keyquesttech/Enclave/imgs/36.PNG

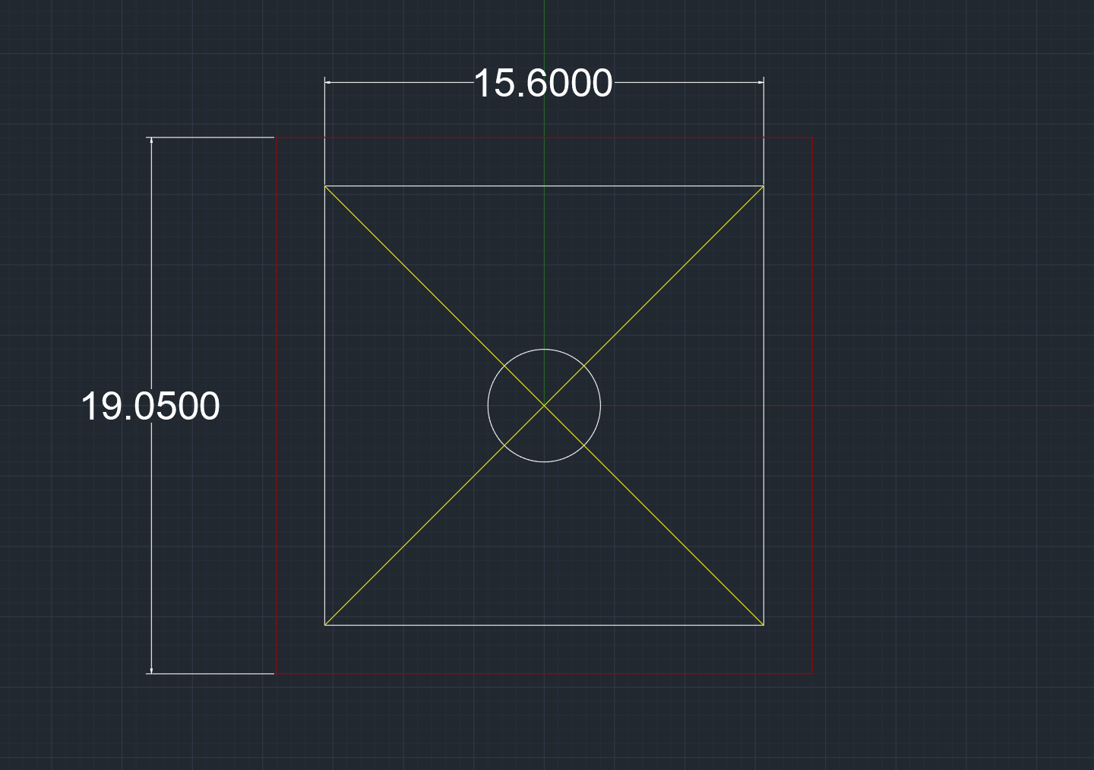
imgs/36.PNG
