keyquesttech/Enclave/imgs/37.PNG

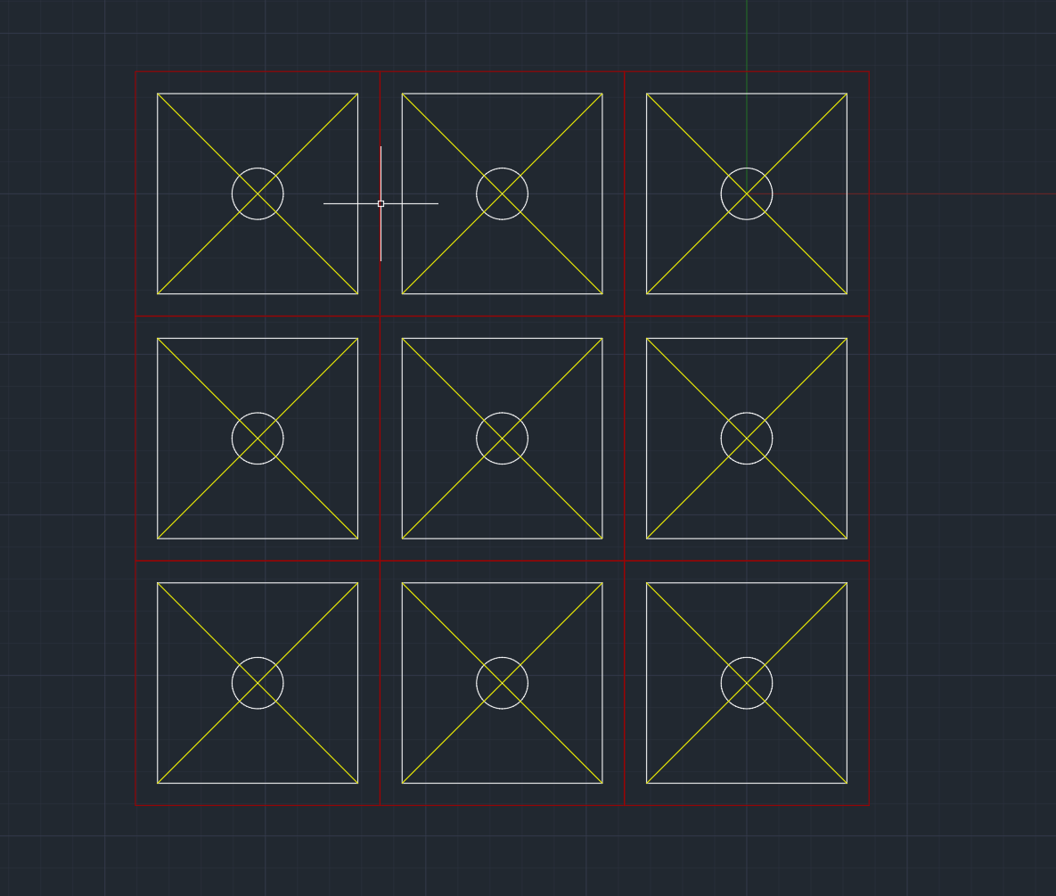
imgs/37.PNG
