keyquesttech/Enclave/imgs/38.PNG

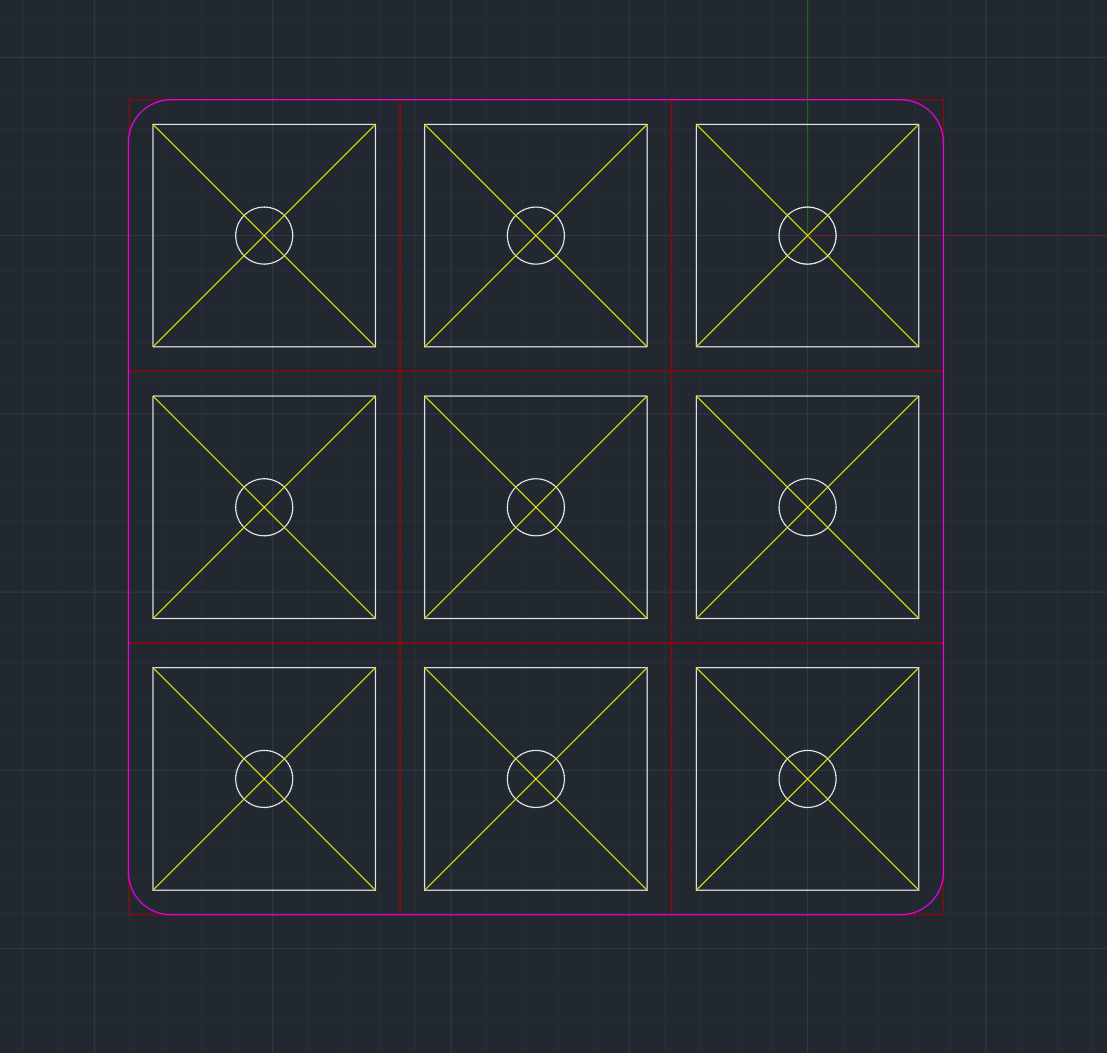
imgs/38.PNG
