keyquesttech/Enclave/imgs/39.PNG

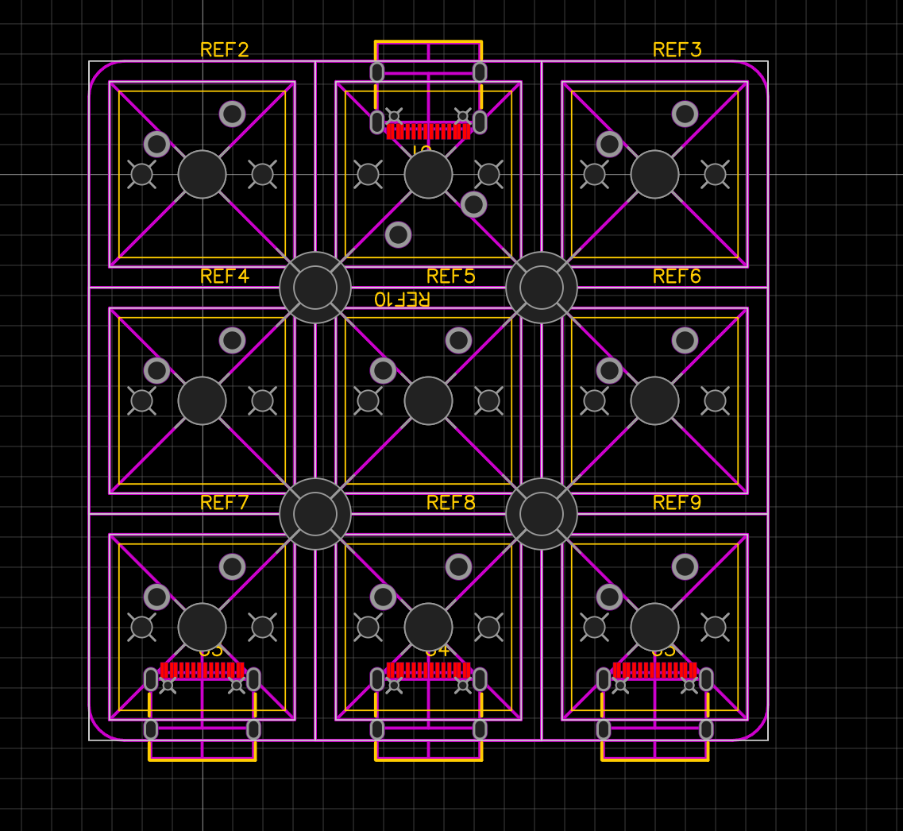
imgs/39.PNG
