keyquesttech/Enclave/imgs/40.PNG

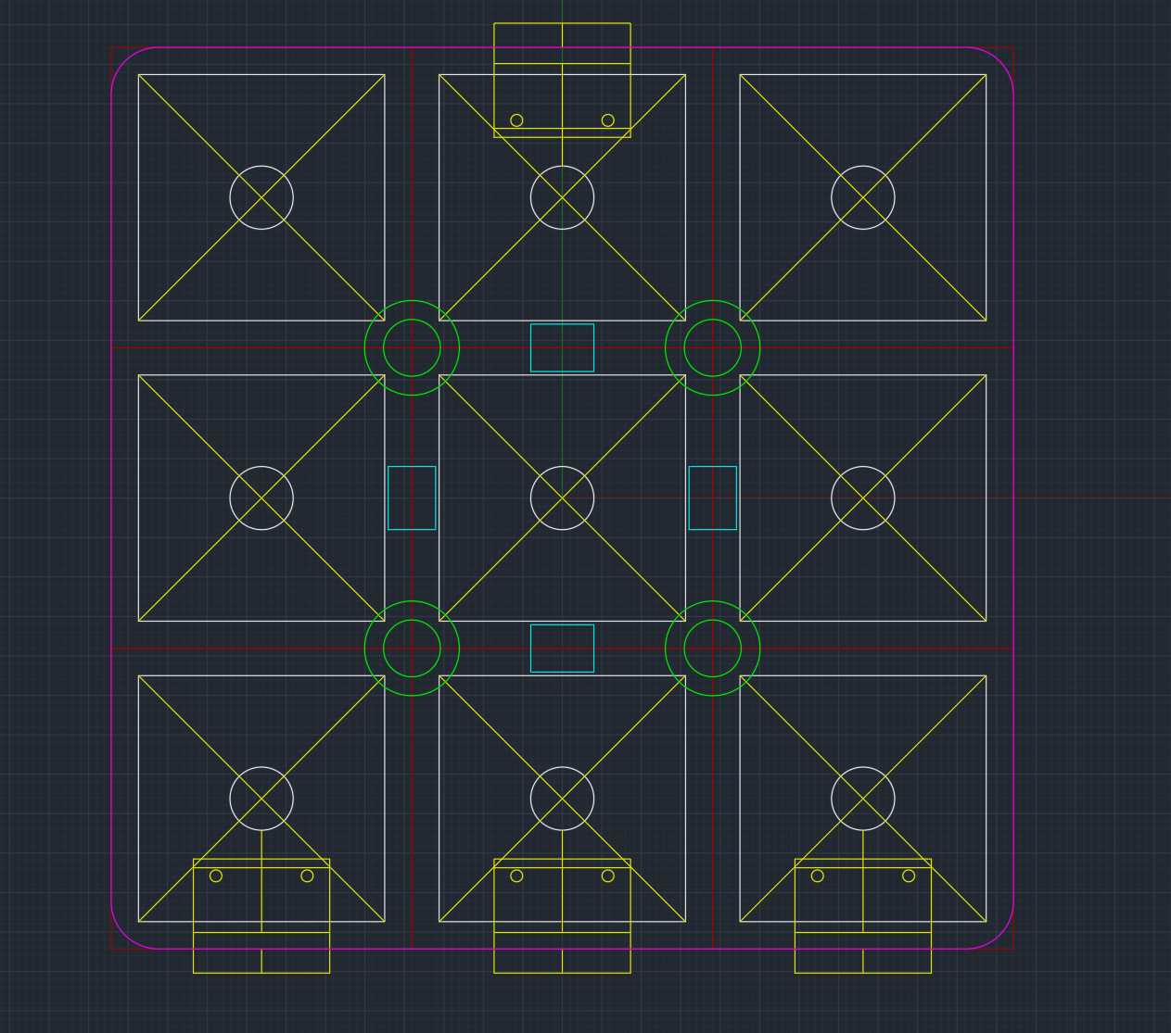
imgs/40.PNG
