keyquesttech/Enclave/imgs/41.jpg

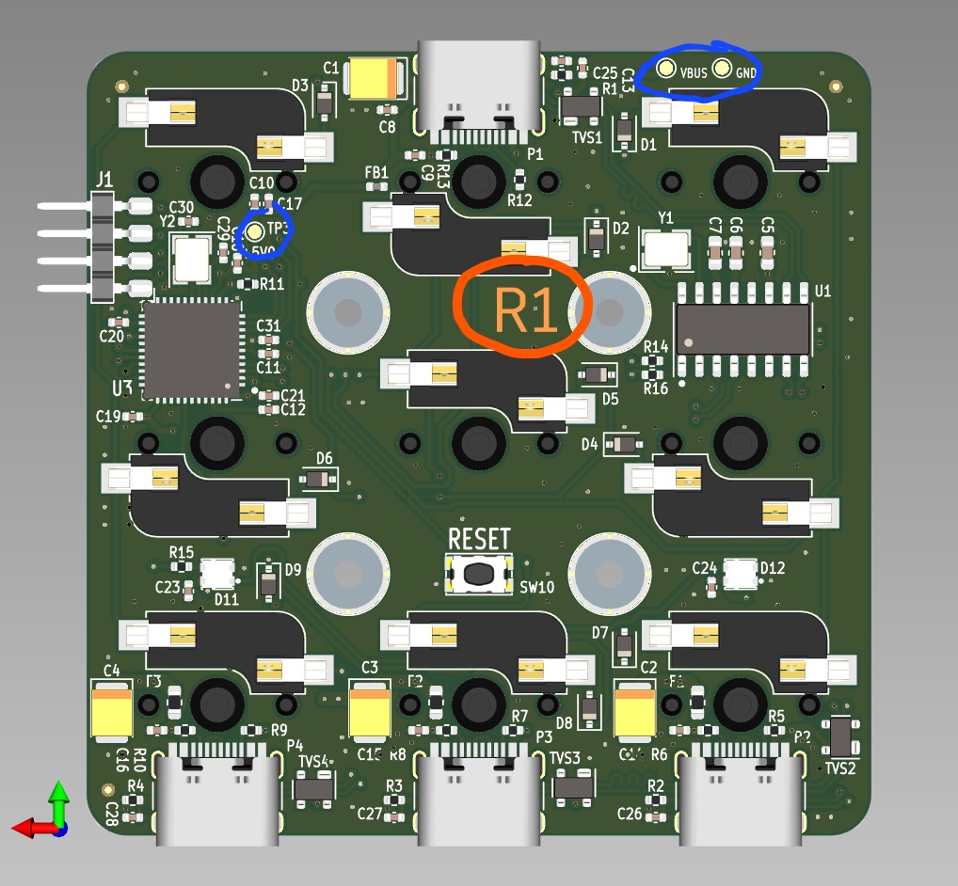
imgs/41.jpg
