keyquesttech/Enclave/imgs/75.jpg

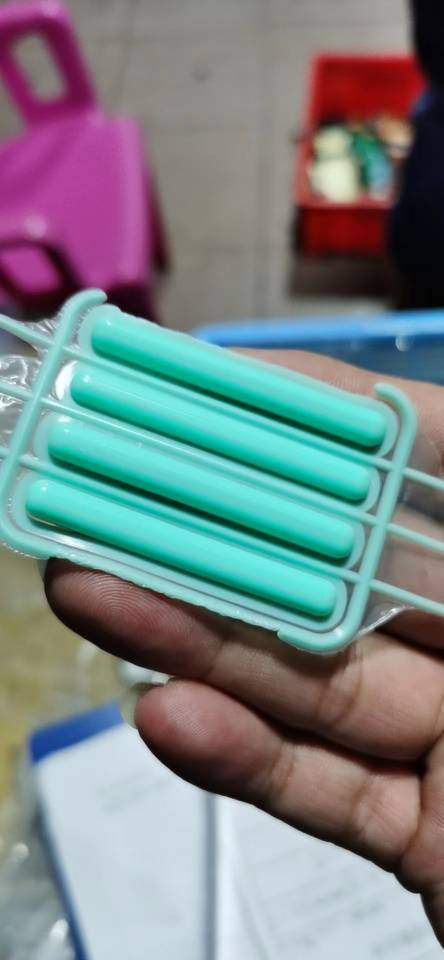
imgs/75.jpg
