keyquesttech/Enclave/imgs/77.png

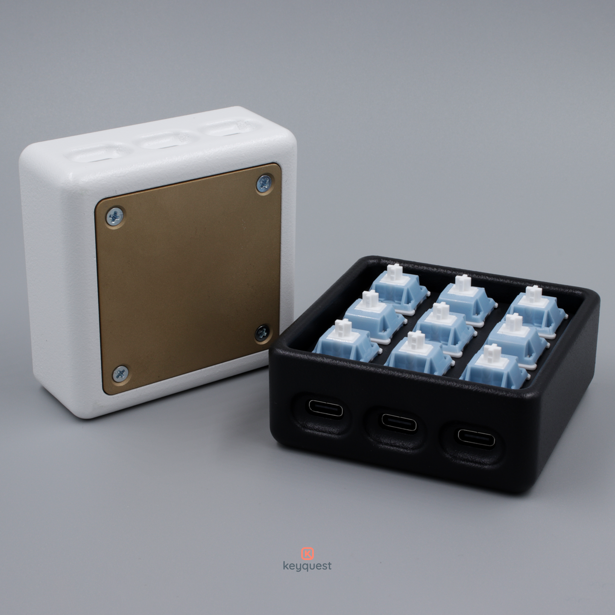
imgs/77.png
