keyquesttech/Enclave/imgs/78.png

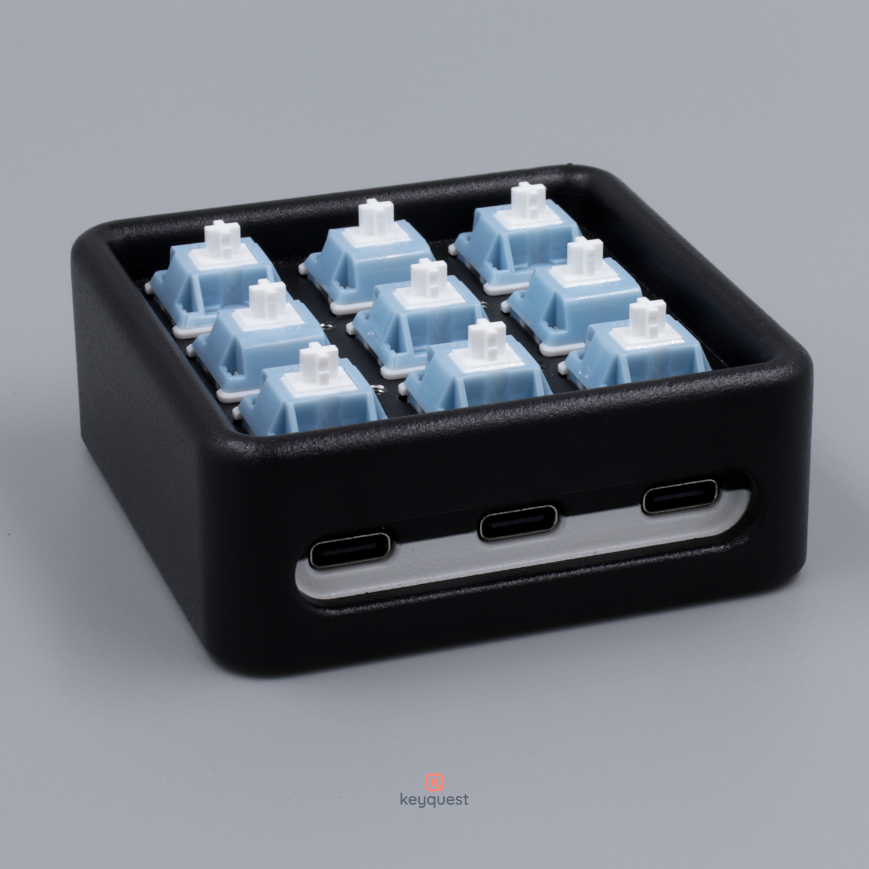
imgs/78.png
