keyquesttech/Enclave/imgs/79.png

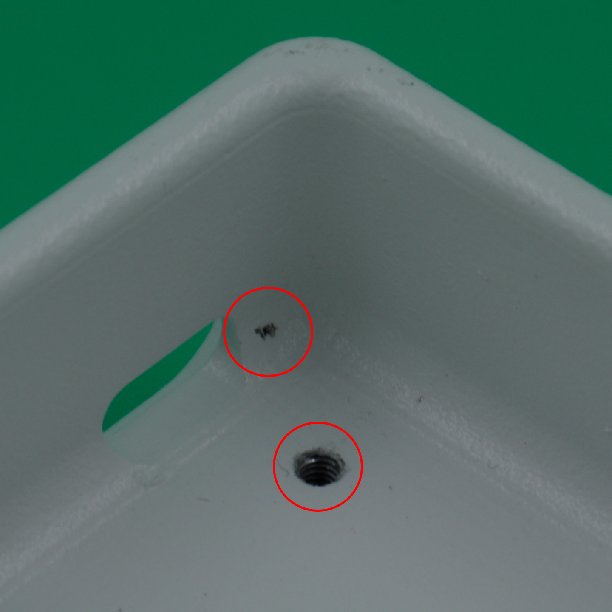
imgs/79.png
