keyquesttech/Enclave/imgs/83.jpg

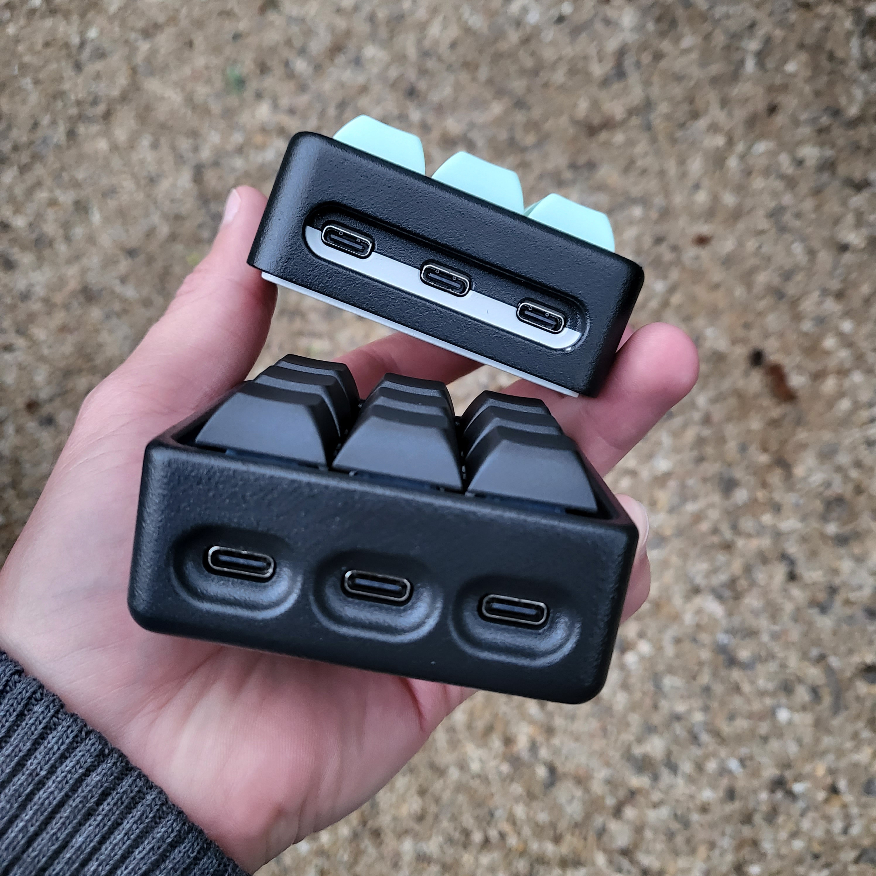
imgs/83.jpg
