keyquesttech/Enclave/imgs/84.PNG

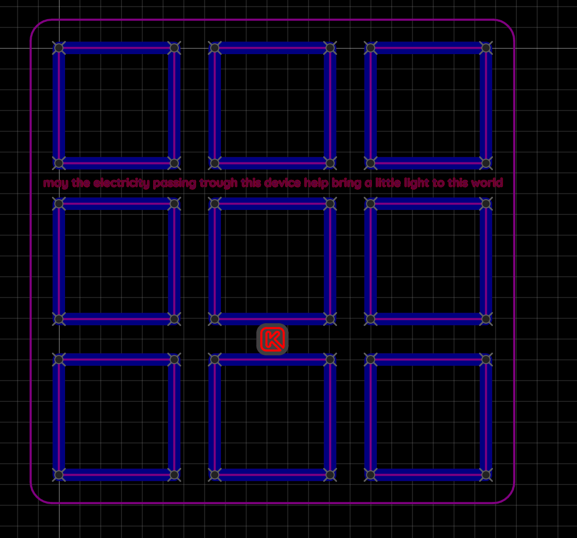
imgs/84.PNG
