keyquesttech/Enclave/imgs/Outline_preview.png

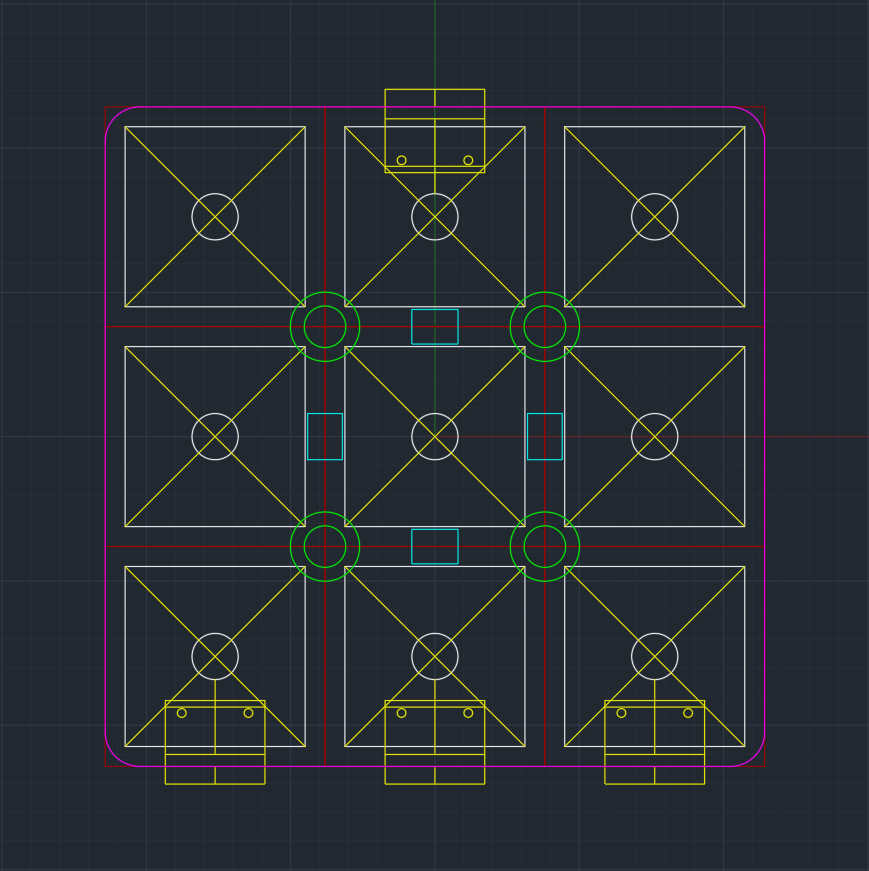
imgs/Outline_preview.png
