keyquesttech/Enclave/imgs/PCB_Mockup.PNG

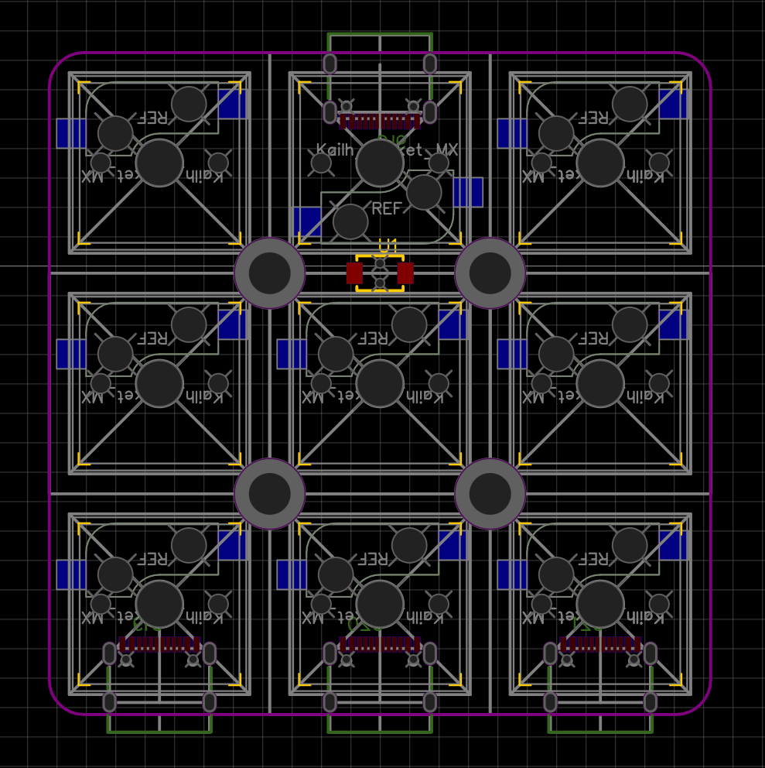
imgs/PCB_Mockup.PNG
