keyquesttech/Enclave/Topo/KiCad_SRC/Topo_v0.kicad_sch

## KiCad design Topo/KiCad_SRC/Topo_v0.kicad_sch (2023-02-13)

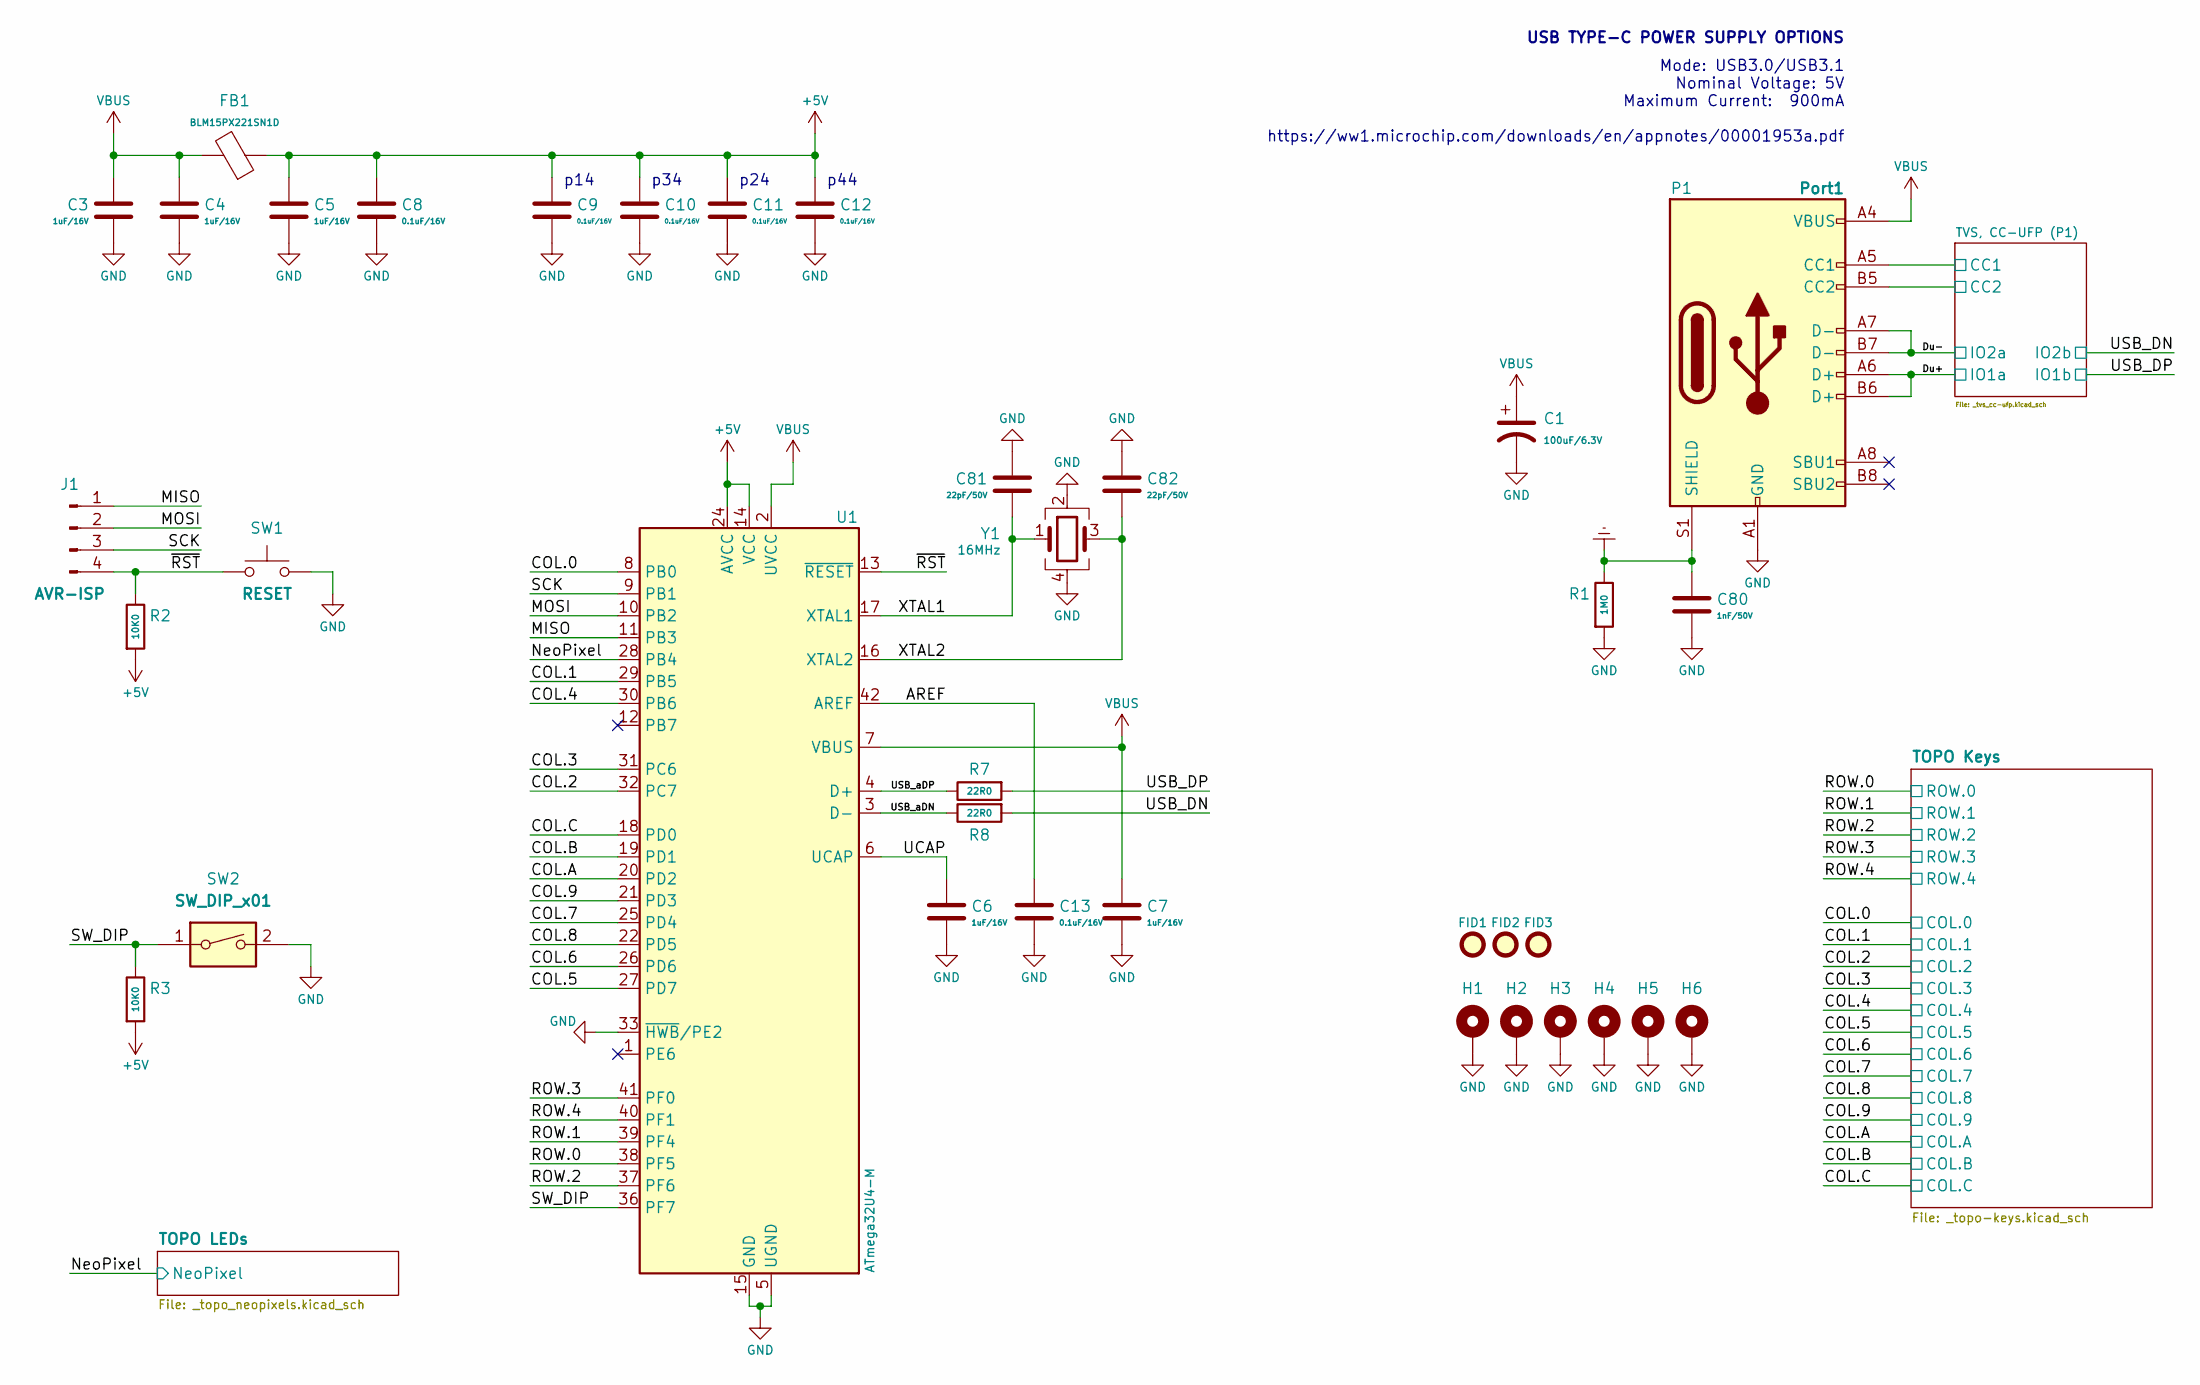
[picture p47: schematic Topo_v0.kicad_sch]

Parts:
C1: 100uF/6.3V; CP_EIA-3528-12_Kemet-T; Part Number TAJB107M006RNJ; Digi-Key 478-3877-1-ND
C3, C4, C5, C6, C7: 1uF/16V; C_0402_1005Metric; Part Number CL05A105KO5NNNC; Digi-Key 1276-1067-1-ND
C8, C9, C10, C11, C12, C13: 0.1uF/16V; C_0402_1005Metric; Part Number CL05B104KO5NNNC; Digi-Key 1276-1001-1-ND
C80: 1nF/50V; C_0402_1005Metric; Part Number CL05B102KB5NNNC; Digi-Key 1276-1032-1-ND
C81, C82: 22pF/50V; C_0402_1005Metric; Part Number CL05C220JB5NNNC; Digi-Key 1276-1116-1-ND
FB1: BLM15PX221SN1D; L_0402_1005Metric; Part Number BLM15PX221SN1D; Digi-Key 490-11021-1-ND
FID1, FID2, FID3: Fiducial; Fiducial_0.5mm_Mask1mm; Part Number - - -; Digi-Key - - -
H1, H2, H3, H4, H5, H6: MountingHole_Pad; Standoff_M2d5_Wurth_9774040151R_mod; Part Number 9774040151R; Digi-Key 732-7089-1-ND
J1: AVR-ISP; PinHeader_1x04_Amphenol_10112684-G03-04ULF_mod; Part Number 10112684-G03-04ULF; Digi-Key 609-4381-ND
P1: Port1; USB_C_Receptacle_HRO_TYPE-C-31-M-12; Part Number TYPE-C-31-M-12; Digi-Key - - -
R1: 1M0; R_0402_1005Metric; Part Number RC0402FR-071ML; Digi-Key 311-1.00MLRCT-ND
R2, R3: 10K0; R_0402_1005Metric; Part Number RC0402FR-0710KL; Digi-Key 311-10.0KLRCT-ND
R7, R8: 22R0; R_0402_1005Metric; Part Number RC0402FR-0722RL; Digi-Key 311-22.0LRCT-ND
SW1: RESET; SW_SPST_CandK_PTS830; Part Number PTS830GM140 SMTR LFS; Digi-Key CKN10587CT-ND
SW2: SW_DIP_x01; SW_DIP_SPSTx01_Slide_CUI_DS04-254-1-01BK-SMT_W6.20mm_P2.54mm; Part Number DS04-254-1-01BK-SMT; Digi-Key 2223-DS04-254-1-01BK-SMT-ND
U1: ATmega32U4-M; QFN-44-1EP_7x7mm_P0.5mm_EP5.2x5.2mm; Part Number ATMEGA32U4-MUR; Digi-Key ATMEGA32U4-MURCT-ND
Y1: 16MHz; Crystal_SMD_Abracon_ABM8G-4Pin_3.2x2.5mm; Part Number ABM8G-16.000MHZ-18-D2Y-T; Digi-Key 535-10267-1-ND

Connections:
+5V: C5.2, C8.1, C9.1, C10.1, C11.1, C12.1, FB1.1, R2.2, R3.2, U1.14 (VCC), U1.24 (AVCC), U1.34 (VCC), U1.44 (AVCC)
AREF: C13.1, U1.42 (AREF)
CC1: P1.A5 (CC1)
CC2: P1.B5 (CC2)
COL.0: U1.8 (PB0)
COL.1: U1.29 (PB5)
COL.2: U1.32 (PC7)
COL.3: U1.31 (PC6)
COL.4: U1.30 (PB6)
COL.5: U1.27 (PD7)
COL.6: U1.26 (PD6)
COL.7: U1.25 (PD4)
COL.8: U1.22 (PD5)
COL.9: U1.21 (PD3)
COL.A: U1.20 (PD2)
COL.B: U1.19 (PD1)
COL.C: U1.18 (PD0)
Du+: P1.A6 (D+), P1.B6 (D+)
Du-: P1.A7 (D-), P1.B7 (D-)
Earth: C80.1, P1.S1 (SHIELD), R1.1
GND: C1.2, C3.2, C4.1, C5.1, C6.1, C7.1, C8.2, C9.2, C10.2, C11.2, C12.2, C13.2, C80.2, C81.1, C82.1, H1.1, H2.1, H3.1, H4.1, H5.1, H6.1, P1.A1 (GND), P1.A12 (GND), P1.B1 (GND), P1.B12 (GND), R1.2, SW1.1, SW2.2, U1.5 (UGND), U1.15 (GND), U1.23 (GND), U1.33 (~HWB/PE2), U1.35 (GND), U1.43 (GND), U1.45 (GND), Y1.2, Y1.4
MISO: J1.1, U1.11 (PB3)
MOSI: J1.2, U1.10 (PB2)
NeoPixel: U1.28 (PB4)
ROW.0: U1.38 (PF5)
ROW.1: U1.39 (PF4)
ROW.2: U1.37 (PF6)
ROW.3: U1.41 (PF0)
ROW.4: U1.40 (PF1)
SCK: J1.3, U1.9 (PB1)
SW_DIP: R3.1, SW2.1, U1.36 (PF7)
UCAP: C6.2, U1.6 (UCAP)
USB_DN: R8.2
USB_DP: R7.2
USB_aDN: R8.1, U1.3 (D-)
USB_aDP: R7.1, U1.4 (D+)
VBUS: C1.1, C3.1, C4.2, C7.2, FB1.2, P1.A4 (VBUS), P1.A9 (VBUS), P1.B4 (VBUS), P1.B9 (VBUS), U1.2 (UVCC), U1.7 (VBUS)
XTAL1: C81.2, U1.17 (XTAL1), Y1.1
XTAL2: C82.2, U1.16 (XTAL2), Y1.3
~RST: J1.4, R2.1, SW1.2, U1.13 (~RESET)

Notes on the sheet:
p24
p34
USB TYPE-C POWER SUPPLY OPTIONS
p14
Mode: USB3.0/USB3.1 Nominal Voltage: 5V Maximum Current: 900mA https://ww1.microchip.com/downloads/en/appnotes/00001953a.pdf
p44
