keyquesttech/Enclave/Topo/KiCad_SRC/_topo-keys.kicad_sch

## KiCad design Topo/KiCad_SRC/_topo-keys.kicad_sch (2023-02-13)

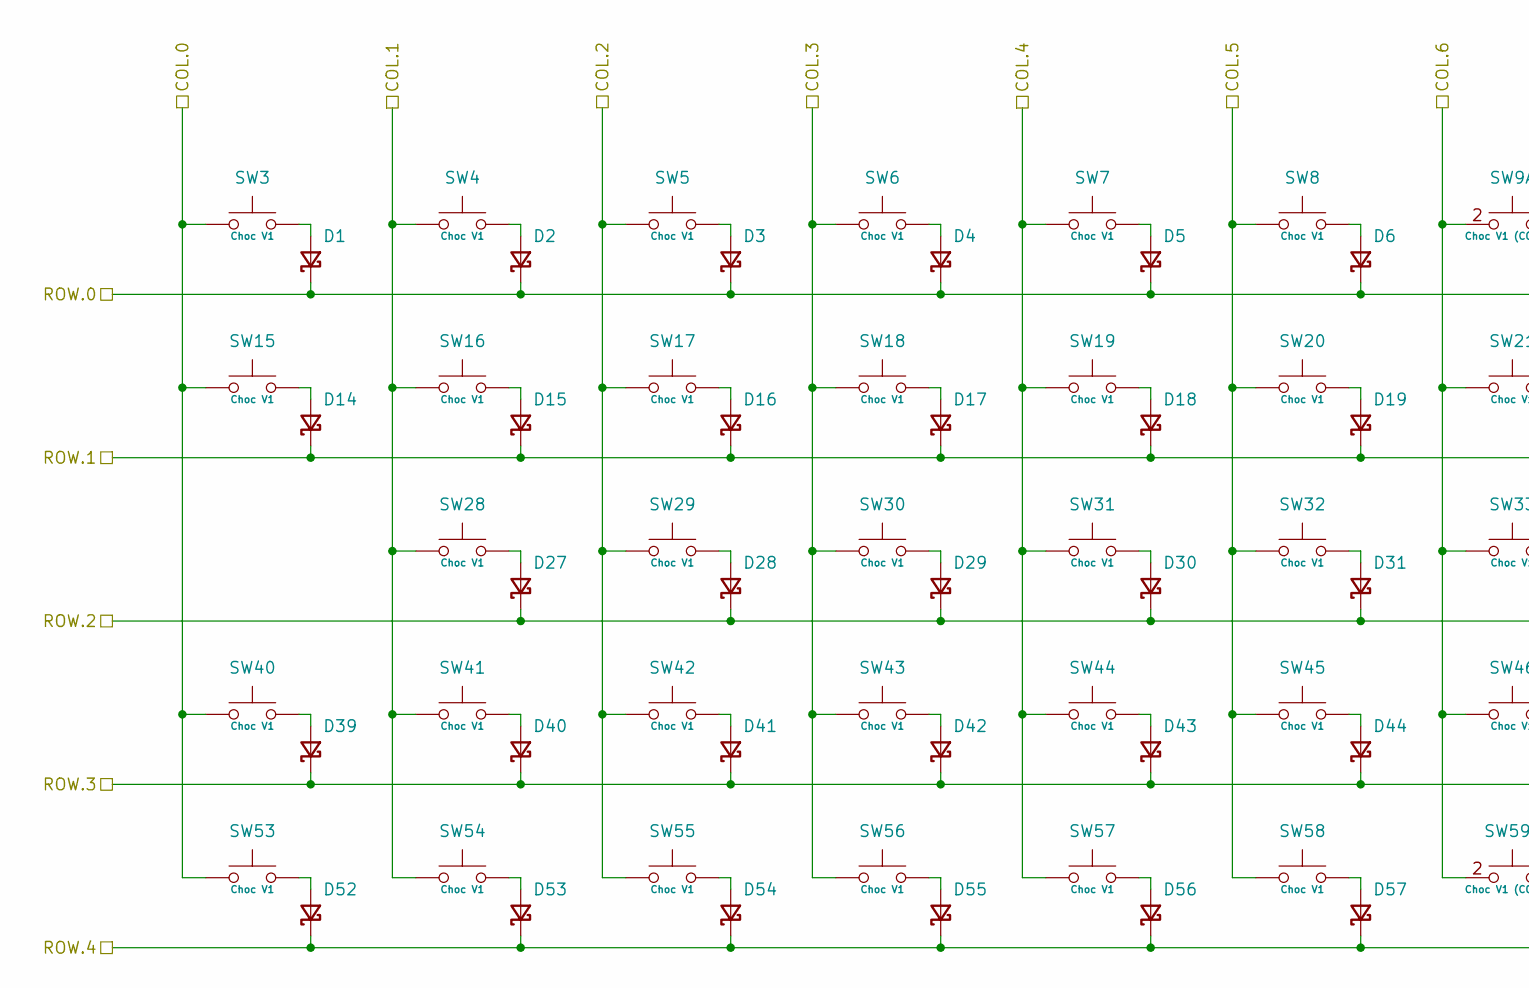
[picture p48: schematic _topo-keys.kicad_sch, part in row 1, column 1]

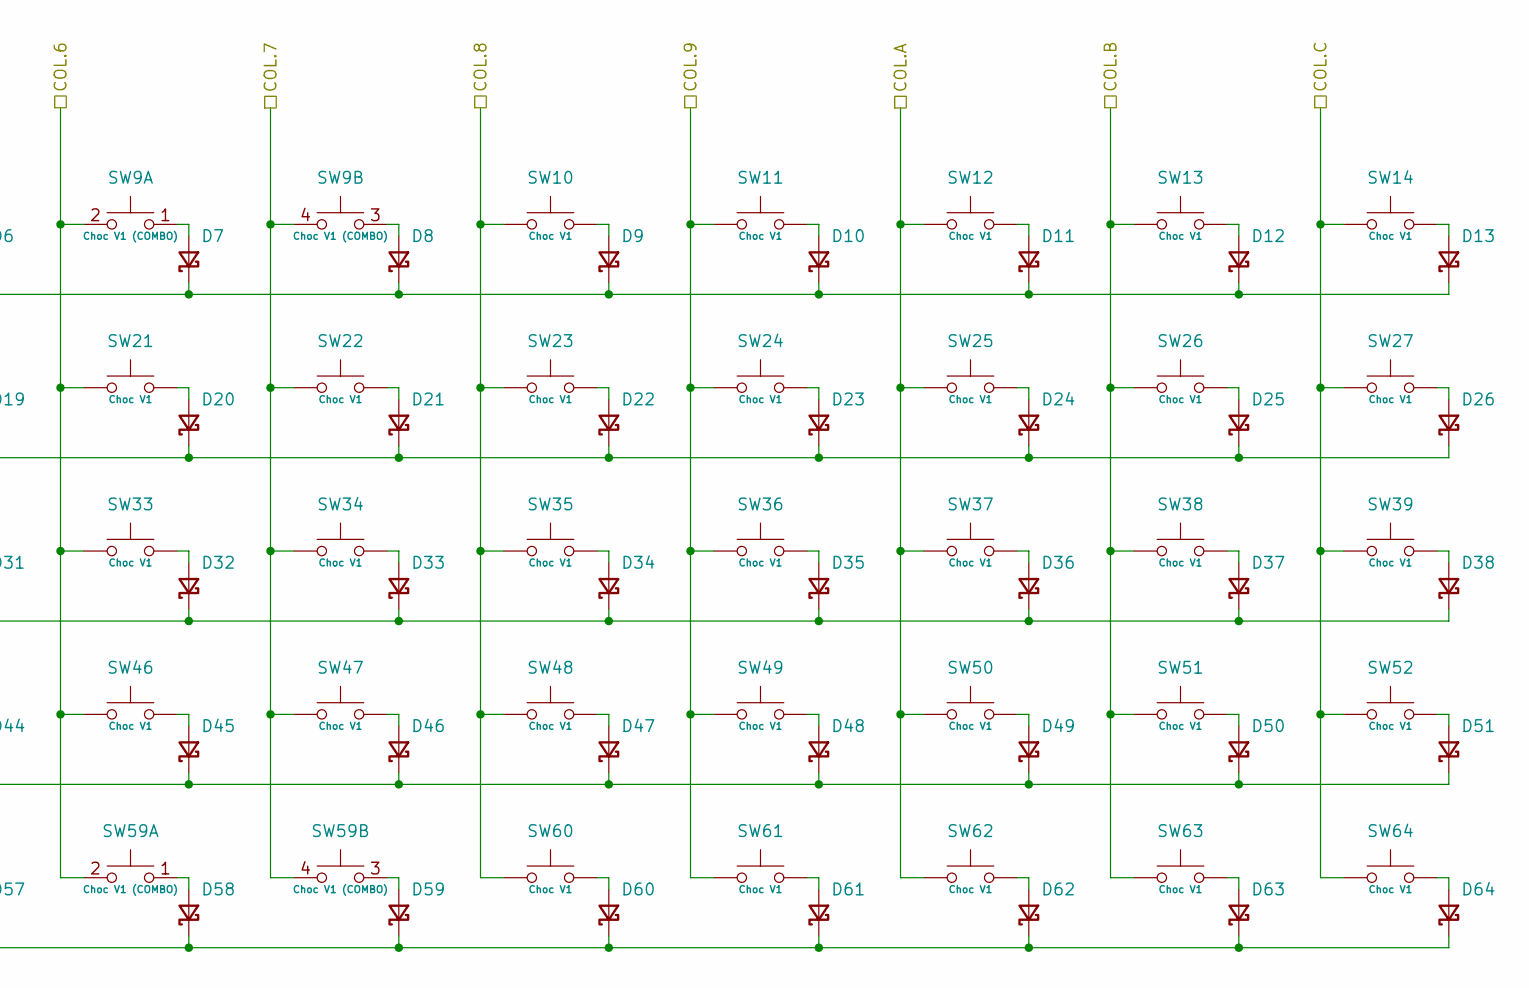
[picture p49: schematic _topo-keys.kicad_sch, part in row 1, column 2]

Parts:
D1, D2, D3, D4, D5, D6, D7, D8, D9, D10, D11, D12, D13, D14, D15, D16, D17, D18, D19, D20, D21, D22, D23, D24, D25, D26, D27, D28, D29, D30, D31, D32, D33, D34, D35, D36, D37, D38, D39, D40, D41, D42, D43, D44, D45, D46, D47, D48, D49, D50, D51, D52, D53, D54, D55, D56, D57, D58, D59, D60, D61, D62, D63, D64: SD103AWS-TP; D_SOD-323; Part Number SD103AWS-TP; Digi-Key SD103AWSTPMSCT-ND
SW3, SW4, SW5, SW6, SW7, SW8, SW10, SW11, SW12, SW13, SW14, SW15, SW16, SW17, SW18, SW19, SW20, SW21, SW22, SW23, SW24, SW25, SW26, SW27, SW28, SW29, SW30, SW31, SW32, SW33, SW34, SW35, SW36, SW37, SW38, SW39, SW40, SW41, SW42, SW43, SW44, SW45, SW46, SW47, SW48, SW49, SW50, SW51, SW52, SW53, SW54, SW55, SW56, SW57, SW58, SW60, SW61, SW62, SW63, SW64: Choc V1; SW_Kailh_CPG135001D01-1U; Part Number Cherry MX; Digi-Key - - -
SW9, SW59: Choc V1 (COMBO); SW_Kailh_CPG135001D01-1U2Ucombo; Part Number Cherry MX; Digi-Key - - -

Connections:
COL.0: SW3.2, SW15.2, SW40.2, SW53.2
COL.1: SW4.2, SW16.2, SW28.2, SW41.2, SW54.2
COL.2: SW5.2, SW17.2, SW29.2, SW42.2, SW55.2
COL.3: SW6.2, SW18.2, SW30.2, SW43.2, SW56.2
COL.4: SW7.2, SW19.2, SW31.2, SW44.2, SW57.2
COL.5: SW8.2, SW20.2, SW32.2, SW45.2, SW58.2
COL.6: SW9.2 (D), SW21.2, SW33.2, SW46.2, SW59.2 (D)
COL.7: SW9.4 (D), SW22.2, SW34.2, SW47.2, SW59.4 (D)
COL.8: SW10.2, SW23.2, SW35.2, SW48.2, SW60.2
COL.9: SW11.2, SW24.2, SW36.2, SW49.2, SW61.2
COL.A: SW12.2, SW25.2, SW37.2, SW50.2, SW62.2
COL.B: SW13.2, SW26.2, SW38.2, SW51.2, SW63.2
COL.C: SW14.2, SW27.2, SW39.2, SW52.2, SW64.2
unnamed: D1.2 (A), SW3.1
unnamed: D2.2 (A), SW4.1
unnamed: D3.2 (A), SW5.1
unnamed: D4.2 (A), SW6.1
unnamed: D5.2 (A), SW7.1
unnamed: D6.2 (A), SW8.1
unnamed: D7.2 (A), SW9.1 (C)
unnamed: D8.2 (A), SW9.3 (C)
unnamed: D9.2 (A), SW10.1
unnamed: D10.2 (A), SW11.1
unnamed: D11.2 (A), SW12.1
unnamed: D12.2 (A), SW13.1
unnamed: D13.2 (A), SW14.1
unnamed: D14.2 (A), SW15.1
unnamed: D15.2 (A), SW16.1
unnamed: D16.2 (A), SW17.1
unnamed: D17.2 (A), SW18.1
unnamed: D18.2 (A), SW19.1
unnamed: D19.2 (A), SW20.1
unnamed: D20.2 (A), SW21.1
unnamed: D21.2 (A), SW22.1
unnamed: D22.2 (A), SW23.1
unnamed: D23.2 (A), SW24.1
unnamed: D24.2 (A), SW25.1
unnamed: D25.2 (A), SW26.1
unnamed: D26.2 (A), SW27.1
unnamed: D27.2 (A), SW28.1
unnamed: D28.2 (A), SW29.1
unnamed: D29.2 (A), SW30.1
unnamed: D30.2 (A), SW31.1
unnamed: D31.2 (A), SW32.1
unnamed: D32.2 (A), SW33.1
unnamed: D33.2 (A), SW34.1
unnamed: D34.2 (A), SW35.1
unnamed: D35.2 (A), SW36.1
unnamed: D36.2 (A), SW37.1
unnamed: D37.2 (A), SW38.1
unnamed: D38.2 (A), SW39.1
unnamed: D39.2 (A), SW40.1
unnamed: D40.2 (A), SW41.1
unnamed: D41.2 (A), SW42.1
unnamed: D42.2 (A), SW43.1
unnamed: D43.2 (A), SW44.1
unnamed: D44.2 (A), SW45.1
unnamed: D45.2 (A), SW46.1
unnamed: D46.2 (A), SW47.1
unnamed: D47.2 (A), SW48.1
unnamed: D48.2 (A), SW49.1
unnamed: D49.2 (A), SW50.1
unnamed: D50.2 (A), SW51.1
unnamed: D51.2 (A), SW52.1
unnamed: D52.2 (A), SW53.1
unnamed: D53.2 (A), SW54.1
unnamed: D54.2 (A), SW55.1
unnamed: D55.2 (A), SW56.1
unnamed: D56.2 (A), SW57.1
unnamed: D57.2 (A), SW58.1
unnamed: D58.2 (A), SW59.1 (C)
unnamed: D59.2 (A), SW59.3 (C)
unnamed: D60.2 (A), SW60.1
unnamed: D61.2 (A), SW61.1
unnamed: D62.2 (A), SW62.1
unnamed: D63.2 (A), SW63.1
unnamed: D64.2 (A), SW64.1
ROW.0: D1.1 (K), D2.1 (K), D3.1 (K), D4.1 (K), D5.1 (K), D6.1 (K), D7.1 (K), D8.1 (K), D9.1 (K), D10.1 (K), D11.1 (K), D12.1 (K), D13.1 (K)
ROW.1: D14.1 (K), D15.1 (K), D16.1 (K), D17.1 (K), D18.1 (K), D19.1 (K), D20.1 (K), D21.1 (K), D22.1 (K), D23.1 (K), D24.1 (K), D25.1 (K), D26.1 (K)
ROW.2: D27.1 (K), D28.1 (K), D29.1 (K), D30.1 (K), D31.1 (K), D32.1 (K), D33.1 (K), D34.1 (K), D35.1 (K), D36.1 (K), D37.1 (K), D38.1 (K)
ROW.3: D39.1 (K), D40.1 (K), D41.1 (K), D42.1 (K), D43.1 (K), D44.1 (K), D45.1 (K), D46.1 (K), D47.1 (K), D48.1 (K), D49.1 (K), D50.1 (K), D51.1 (K)
ROW.4: D52.1 (K), D53.1 (K), D54.1 (K), D55.1 (K), D56.1 (K), D57.1 (K), D58.1 (K), D59.1 (K), D60.1 (K), D61.1 (K), D62.1 (K), D63.1 (K), D64.1 (K)
