keyquesttech/Enclave/Topo/KiCad_SRC/_topo_neopixels.kicad_sch

## KiCad design Topo/KiCad_SRC/_topo_neopixels.kicad_sch (2023-02-13)

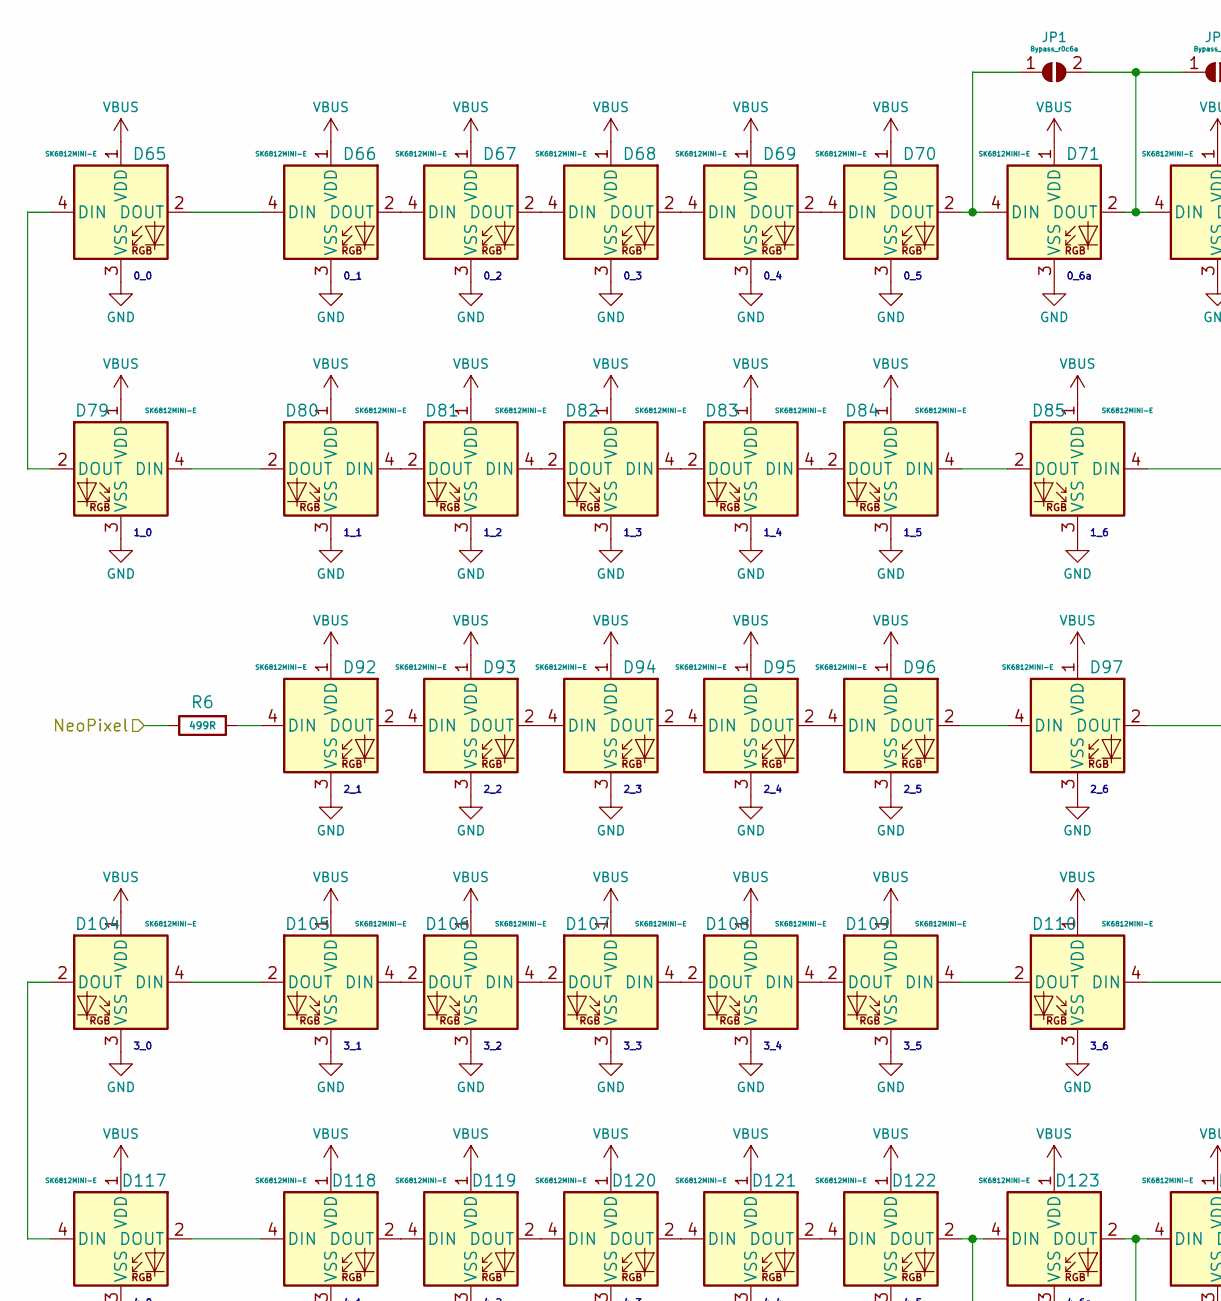
[picture p50: schematic _topo_neopixels.kicad_sch, part in row 1, column 1]

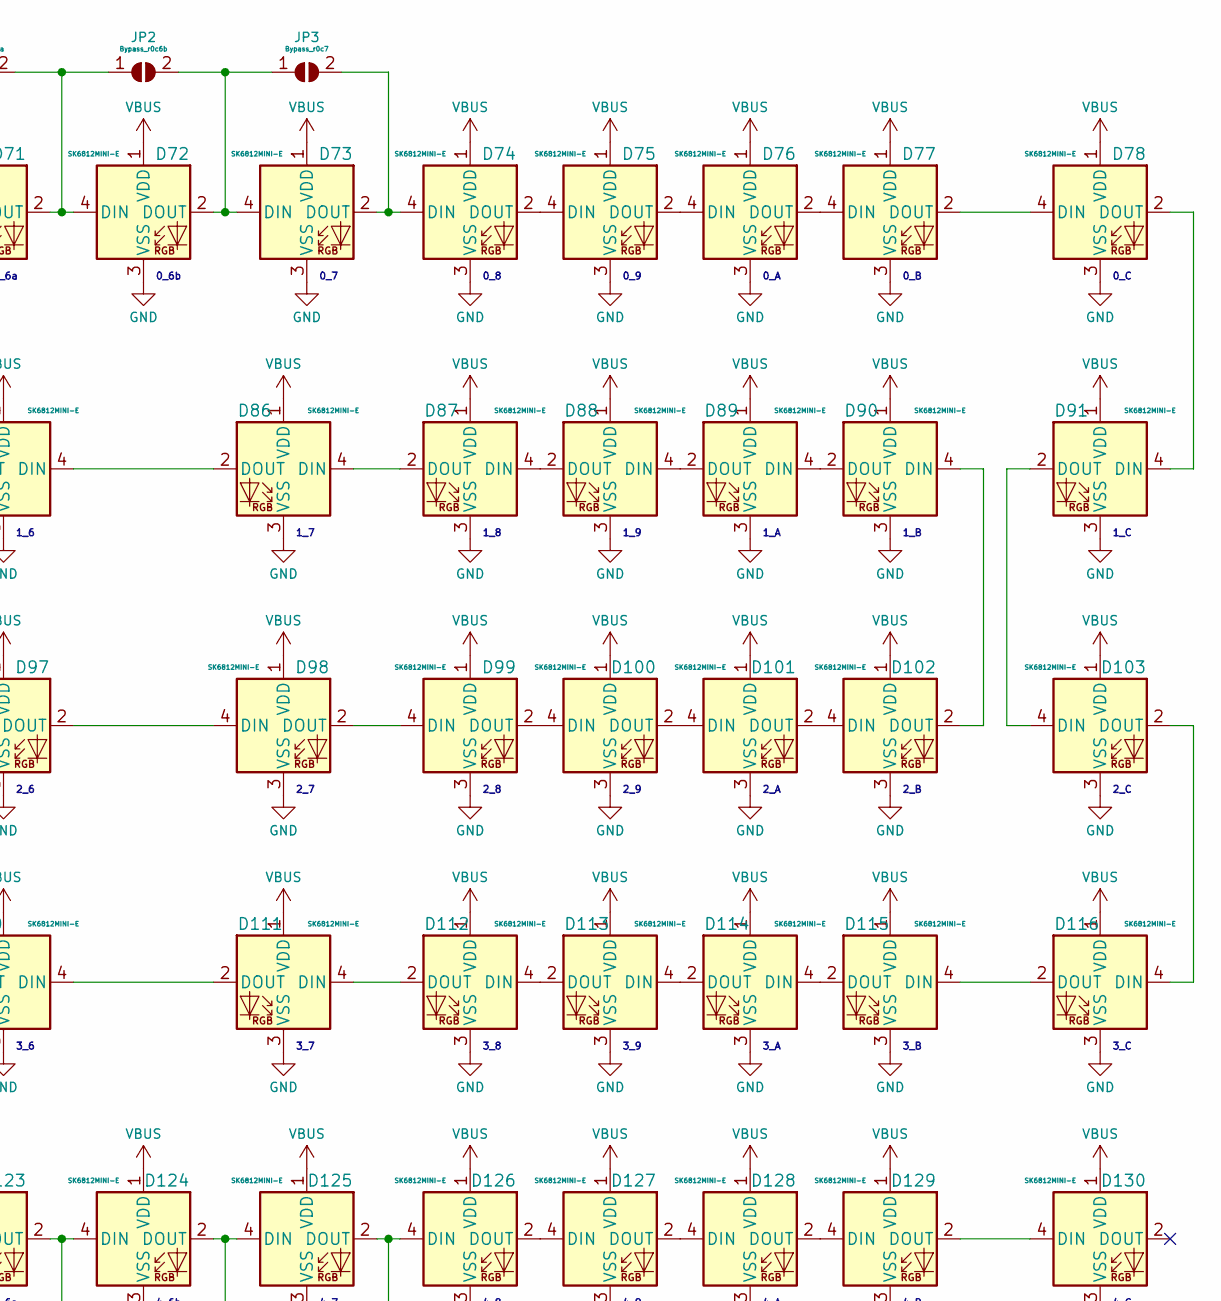
[picture p51: schematic _topo_neopixels.kicad_sch, part in row 1, column 2]

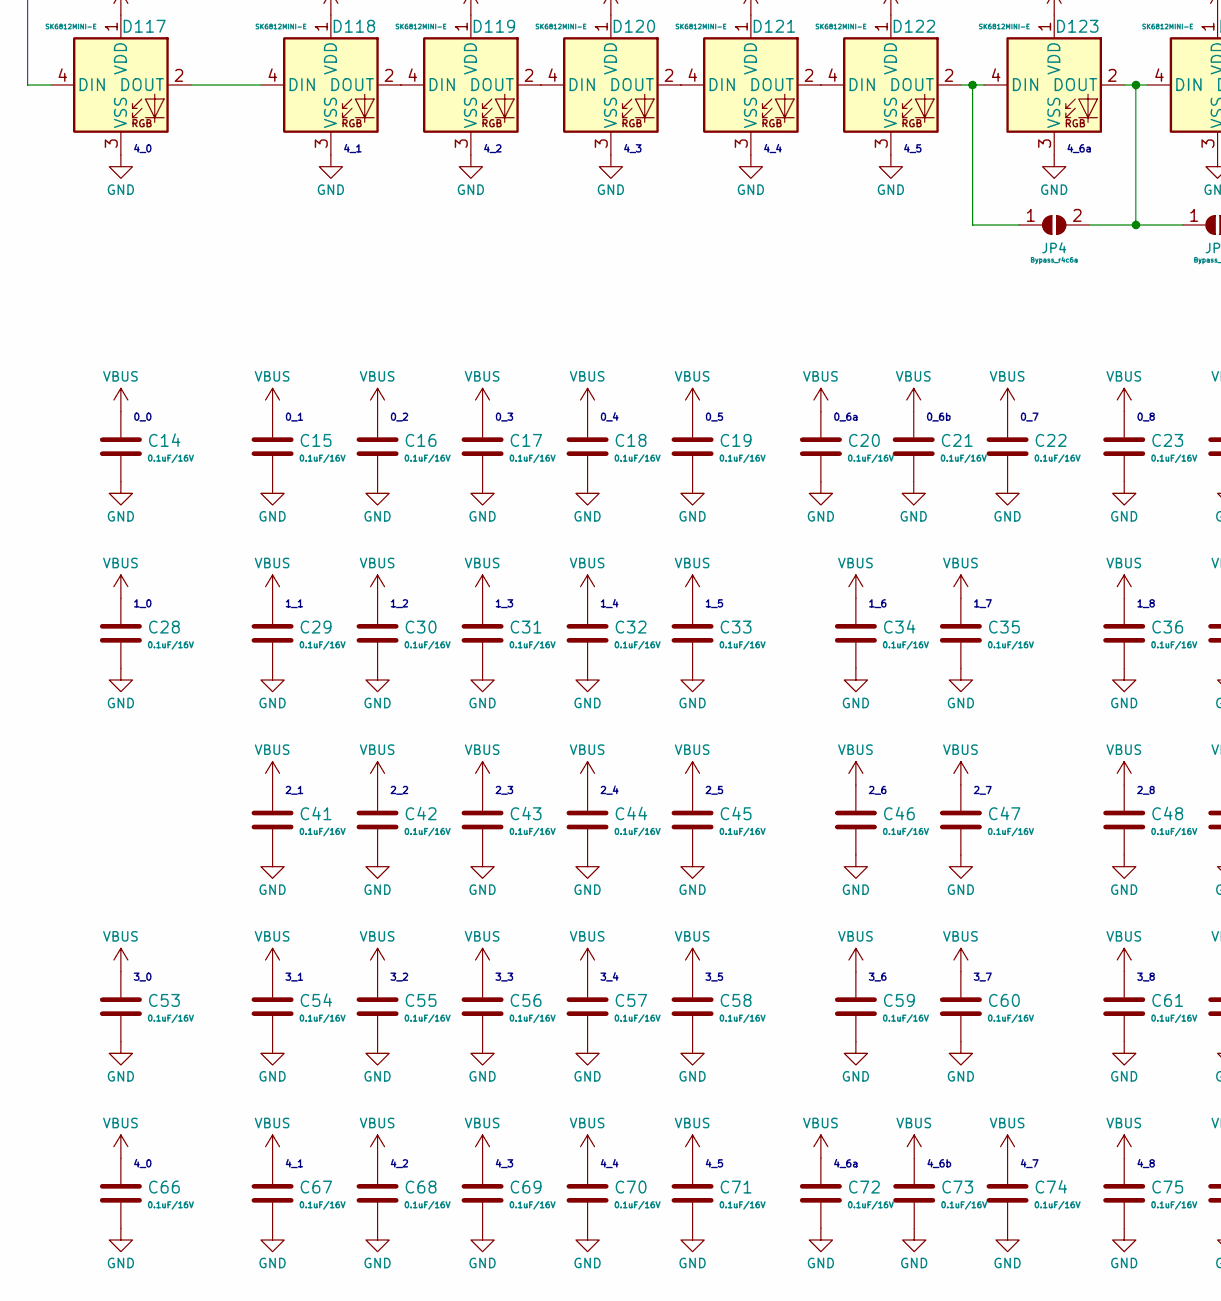
[picture p52: schematic _topo_neopixels.kicad_sch, part in row 2, column 1]

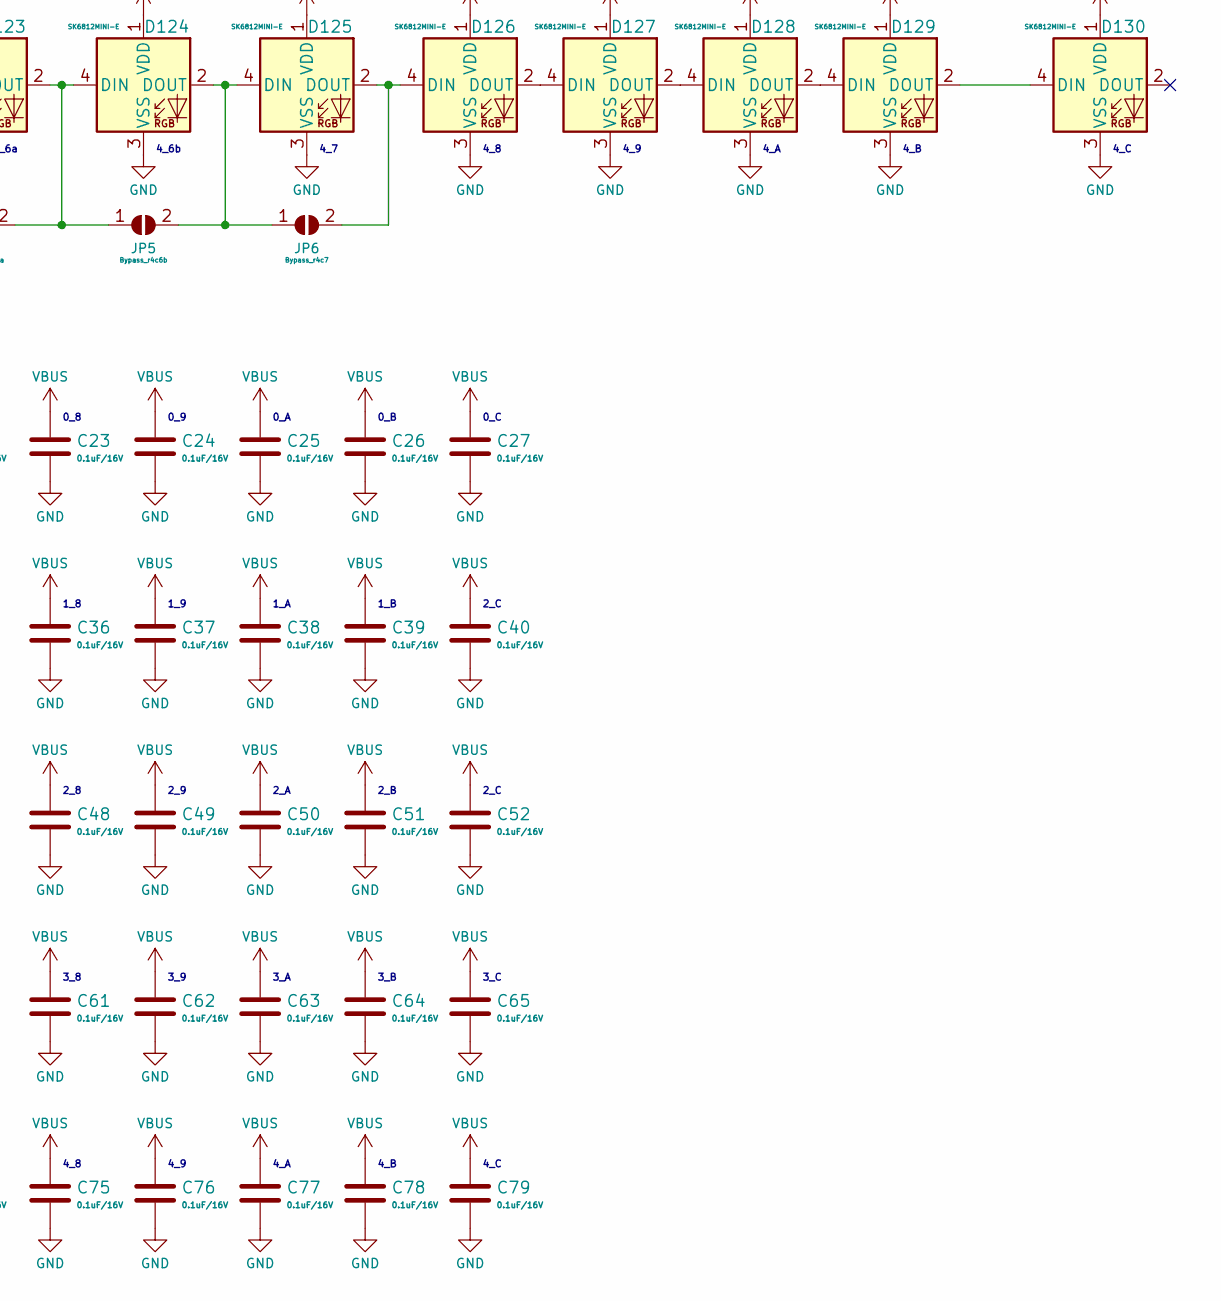
[picture p53: schematic _topo_neopixels.kicad_sch, part in row 2, column 2]

Parts:
C14, C15, C16, C17, C18, C19, C20, C21, C22, C23, C24, C25, C26, C27, C28, C29, C30, C31, C32, C33, C34, C35, C36, C37, C38, C39, C40, C41, C42, C43, C44, C45, C46, C47, C48, C49, C50, C51, C52, C53, C54, C55, C56, C57, C58, C59, C60, C61, C62, C63, C64, C65, C66, C67, C68, C69, C70, C71, C72, C73, C74, C75, C76, C77, C78, C79: 0.1uF/16V; C_0402_1005Metric; Part Number CL05B104KO5NNNC; Digi-Key 1276-1001-1-ND
D65, D66, D67, D68, D69, D70, D71, D72, D73, D74, D75, D76, D77, D78, D79, D80, D81, D82, D83, D84, D85, D86, D87, D88, D89, D90, D91, D92, D93, D94, D95, D96, D97, D98, D99, D100, D101, D102, D103, D104, D105, D106, D107, D108, D109, D110, D111, D112, D113, D114, D115, D116, D117, D118, D119, D120, D121, D122, D123, D124, D125, D126, D127, D128, D129, D130: SK6812MINI-E; LED_OPSCO-Optoelectronics_SK6812MINI-E; Part Number 4960; Digi-Key 1528-4960-ND
JP1: Bypass_r0c6a; uSolderJumper-2P_nRF_NO; Part Number - - -; Digi-Key - - -
JP2: Bypass_r0c6b; uSolderJumper-2P_nRF_NO; Part Number - - -; Digi-Key - - -
JP3: Bypass_r0c7; uSolderJumper-2P_nRF_NO; Part Number - - -; Digi-Key - - -
JP4: Bypass_r4c6a; uSolderJumper-2P_nRF_NO; Part Number - - -; Digi-Key - - -
JP5: Bypass_r4c6b; uSolderJumper-2P_nRF_NO; Part Number - - -; Digi-Key - - -
JP6: Bypass_r4c7; uSolderJumper-2P_nRF_NO; Part Number - - -; Digi-Key - - -
R6: 499R; R_0402_1005Metric; Part Number RC0402FR-07499RL; Digi-Key 311-499LRCT-ND

Connections:
GND: C14.2, C15.2, C16.2, C17.2, C18.2, C19.2, C20.2, C21.2, C22.2, C23.2, C24.2, C25.2, C26.2, C27.2, C28.2, C29.2, C30.2, C31.2, C32.2, C33.2, C34.2, C35.2, C36.2, C37.2, C38.2, C39.2, C40.2, C41.2, C42.2, C43.2, C44.2, C45.2, C46.2, C47.2, C48.2, C49.2, C50.2, C51.2, C52.2, C53.2, C54.2, C55.2, C56.2, C57.2, C58.2, C59.2, C60.2, C61.2, C62.2, C63.2, C64.2, C65.2, C66.2, C67.2, C68.2, C69.2, C70.2, C71.2, C72.2, C73.2, C74.2, C75.2, C76.2, C77.2, C78.2, C79.2, D65.3 (VSS), D66.3 (VSS), D67.3 (VSS), D68.3 (VSS), D69.3 (VSS), D70.3 (VSS), D71.3 (VSS), D72.3 (VSS), D73.3 (VSS), D74.3 (VSS), D75.3 (VSS), D76.3 (VSS), D77.3 (VSS), D78.3 (VSS), D79.3 (VSS), D80.3 (VSS), D81.3 (VSS), D82.3 (VSS), D83.3 (VSS), D84.3 (VSS), D85.3 (VSS), D86.3 (VSS), D87.3 (VSS), D88.3 (VSS), D89.3 (VSS), D90.3 (VSS), D91.3 (VSS), D92.3 (VSS), D93.3 (VSS), D94.3 (VSS), D95.3 (VSS), D96.3 (VSS), D97.3 (VSS), D98.3 (VSS), D99.3 (VSS), D100.3 (VSS), D101.3 (VSS), D102.3 (VSS), D103.3 (VSS), D104.3 (VSS), D105.3 (VSS), D106.3 (VSS), D107.3 (VSS), D108.3 (VSS), D109.3 (VSS), D110.3 (VSS), D111.3 (VSS), D112.3 (VSS), D113.3 (VSS), D114.3 (VSS), D115.3 (VSS), D116.3 (VSS), D117.3 (VSS), D118.3 (VSS), D119.3 (VSS), D120.3 (VSS), D121.3 (VSS), D122.3 (VSS), D123.3 (VSS), D124.3 (VSS), D125.3 (VSS), D126.3 (VSS), D127.3 (VSS), D128.3 (VSS), D129.3 (VSS), D130.3 (VSS)
NeoPixel: R6.1
unnamed: D65.2 (DOUT), D66.4 (DIN)
unnamed: D65.4 (DIN), D79.2 (DOUT)
unnamed: D66.2 (DOUT), D67.4 (DIN)
unnamed: D67.2 (DOUT), D68.4 (DIN)
unnamed: D68.2 (DOUT), D69.4 (DIN)
unnamed: D69.2 (DOUT), D70.4 (DIN)
unnamed: D70.2 (DOUT), D71.4 (DIN), JP1.1 (A)
unnamed: D71.2 (DOUT), D72.4 (DIN), JP1.2 (B), JP2.1 (A)
unnamed: D72.2 (DOUT), D73.4 (DIN), JP2.2 (B), JP3.1 (A)
unnamed: D73.2 (DOUT), D74.4 (DIN), JP3.2 (B)
unnamed: D74.2 (DOUT), D75.4 (DIN)
unnamed: D75.2 (DOUT), D76.4 (DIN)
unnamed: D76.2 (DOUT), D77.4 (DIN)
unnamed: D77.2 (DOUT), D78.4 (DIN)
unnamed: D78.2 (DOUT), D91.4 (DIN)
unnamed: D79.4 (DIN), D80.2 (DOUT)
unnamed: D80.4 (DIN), D81.2 (DOUT)
unnamed: D81.4 (DIN), D82.2 (DOUT)
unnamed: D82.4 (DIN), D83.2 (DOUT)
unnamed: D83.4 (DIN), D84.2 (DOUT)
unnamed: D84.4 (DIN), D85.2 (DOUT)
unnamed: D85.4 (DIN), D86.2 (DOUT)
unnamed: D86.4 (DIN), D87.2 (DOUT)
unnamed: D87.4 (DIN), D88.2 (DOUT)
unnamed: D88.4 (DIN), D89.2 (DOUT)
unnamed: D89.4 (DIN), D90.2 (DOUT)
unnamed: D92.2 (DOUT), D93.4 (DIN)
unnamed: D92.4 (DIN), R6.2
unnamed: D93.2 (DOUT), D94.4 (DIN)
unnamed: D94.2 (DOUT), D95.4 (DIN)
unnamed: D95.2 (DOUT), D96.4 (DIN)
unnamed: D96.2 (DOUT), D97.4 (DIN)
unnamed: D97.2 (DOUT), D98.4 (DIN)
unnamed: D98.2 (DOUT), D99.4 (DIN)
unnamed: D100.2 (DOUT), D101.4 (DIN)
unnamed: D99.2 (DOUT), D100.4 (DIN)
unnamed: D101.2 (DOUT), D102.4 (DIN)
unnamed: D90.4 (DIN), D102.2 (DOUT)
unnamed: D103.2 (DOUT), D116.4 (DIN)
unnamed: D91.2 (DOUT), D103.4 (DIN)
unnamed: D104.2 (DOUT), D117.4 (DIN)
unnamed: D104.4 (DIN), D105.2 (DOUT)
unnamed: D105.4 (DIN), D106.2 (DOUT)
unnamed: D106.4 (DIN), D107.2 (DOUT)
unnamed: D107.4 (DIN), D108.2 (DOUT)
unnamed: D108.4 (DIN), D109.2 (DOUT)
unnamed: D109.4 (DIN), D110.2 (DOUT)
unnamed: D110.4 (DIN), D111.2 (DOUT)
unnamed: D111.4 (DIN), D112.2 (DOUT)
unnamed: D112.4 (DIN), D113.2 (DOUT)
unnamed: D113.4 (DIN), D114.2 (DOUT)
unnamed: D114.4 (DIN), D115.2 (DOUT)
unnamed: D115.4 (DIN), D116.2 (DOUT)
unnamed: D117.2 (DOUT), D118.4 (DIN)
unnamed: D118.2 (DOUT), D119.4 (DIN)
unnamed: D119.2 (DOUT), D120.4 (DIN)
unnamed: D120.2 (DOUT), D121.4 (DIN)
unnamed: D121.2 (DOUT), D122.4 (DIN)
unnamed: D122.2 (DOUT), D123.4 (DIN), JP4.1 (A)
unnamed: D123.2 (DOUT), D124.4 (DIN), JP4.2 (B), JP5.1 (A)
unnamed: D124.2 (DOUT), D125.4 (DIN), JP5.2 (B), JP6.1 (A)
unnamed: D125.2 (DOUT), D126.4 (DIN), JP6.2 (B)
unnamed: D126.2 (DOUT), D127.4 (DIN)
unnamed: D127.2 (DOUT), D128.4 (DIN)
unnamed: D128.2 (DOUT), D129.4 (DIN)
unnamed: D129.2 (DOUT), D130.4 (DIN)
VBUS: C14.1, C15.1, C16.1, C17.1, C18.1, C19.1, C20.1, C21.1, C22.1, C23.1, C24.1, C25.1, C26.1, C27.1, C28.1, C29.1, C30.1, C31.1, C32.1, C33.1, C34.1, C35.1, C36.1, C37.1, C38.1, C39.1, C40.1, C41.1, C42.1, C43.1, C44.1, C45.1, C46.1, C47.1, C48.1, C49.1, C50.1, C51.1, C52.1, C53.1, C54.1, C55.1, C56.1, C57.1, C58.1, C59.1, C60.1, C61.1, C62.1, C63.1, C64.1, C65.1, C66.1, C67.1, C68.1, C69.1, C70.1, C71.1, C72.1, C73.1, C74.1, C75.1, C76.1, C77.1, C78.1, C79.1, D65.1 (VDD), D66.1 (VDD), D67.1 (VDD), D68.1 (VDD), D69.1 (VDD), D70.1 (VDD), D71.1 (VDD), D72.1 (VDD), D73.1 (VDD), D74.1 (VDD), D75.1 (VDD), D76.1 (VDD), D77.1 (VDD), D78.1 (VDD), D79.1 (VDD), D80.1 (VDD), D81.1 (VDD), D82.1 (VDD), D83.1 (VDD), D84.1 (VDD), D85.1 (VDD), D86.1 (VDD), D87.1 (VDD), D88.1 (VDD), D89.1 (VDD), D90.1 (VDD), D91.1 (VDD), D92.1 (VDD), D93.1 (VDD), D94.1 (VDD), D95.1 (VDD), D96.1 (VDD), D97.1 (VDD), D98.1 (VDD), D99.1 (VDD), D100.1 (VDD), D101.1 (VDD), D102.1 (VDD), D103.1 (VDD), D104.1 (VDD), D105.1 (VDD), D106.1 (VDD), D107.1 (VDD), D108.1 (VDD), D109.1 (VDD), D110.1 (VDD), D111.1 (VDD), D112.1 (VDD), D113.1 (VDD), D114.1 (VDD), D115.1 (VDD), D116.1 (VDD), D117.1 (VDD), D118.1 (VDD), D119.1 (VDD), D120.1 (VDD), D121.1 (VDD), D122.1 (VDD), D123.1 (VDD), D124.1 (VDD), D125.1 (VDD), D126.1 (VDD), D127.1 (VDD), D128.1 (VDD), D129.1 (VDD), D130.1 (VDD)

Notes on the sheet:
1_C
2_C
4_6b
4_2
2_3
2_A
2_9
4_9
3_8
0_0
3_B
0_B
2_2
1_1
0_6b
1_4
1_3
3_1
1_5
0_2
0_A
0_1
1_2
0_6a
2_6
2_4
4_4
3_2
0_9
4_0
1_9
2_7
4_8
4_C
1_0
0_C
4_7
4_3
1_8
3_5
0_3
3_A
2_1
4_A
1_7
0_5
1_A
4_6a
4_B
3_4
0_8
4_5
2_B
3_7
3_6
4_1
0_7
3_9
3_0
1_B
1_6
3_3
0_4
2_8
2_5
3_C
