keyquesttech/Enclave/Topo/KiCad_SRC/_tvs_cc-ufp.kicad_sch

## KiCad design Topo/KiCad_SRC/_tvs_cc-ufp.kicad_sch (2023-02-13)

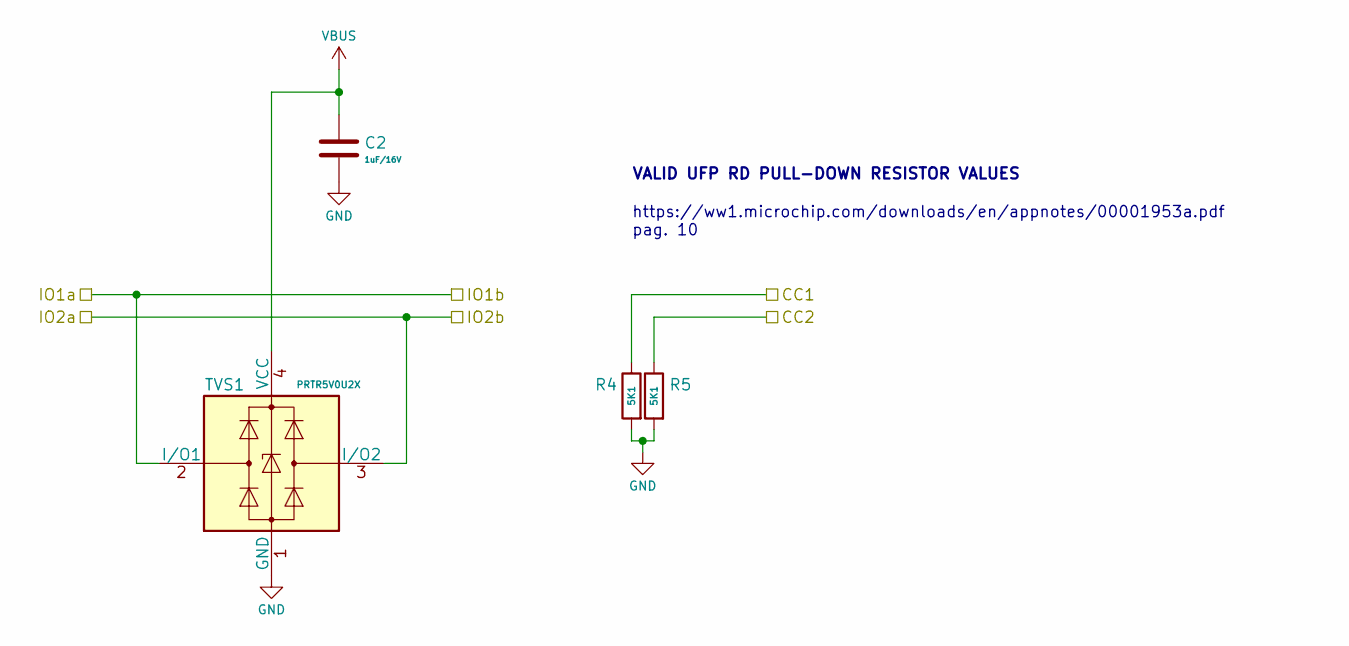
[picture p54: schematic _tvs_cc-ufp.kicad_sch]

Parts:
C2: 1uF/16V; C_0402_1005Metric; Part Number CL05A105KO5NNNC; Digi-Key 1276-1067-1-ND
R4, R5: 5K1; R_0402_1005Metric; Part Number RC0402FR-075K1L; Digi-Key 311-5.10KLRCT-ND
TVS1: PRTR5V0U2X; SOT-143; Part Number PRTR5V0U2X,215; Digi-Key 1727-3884-1-ND

Connections:
CC1: R4.1
CC2: R5.1
GND: C2.2, R4.2, R5.2, TVS1.1 (GND)
IO1a: TVS1.2 (I/O1)
IO2a: TVS1.3 (I/O2)
VBUS: C2.1, TVS1.4 (VCC)

Notes on the sheet:
https://ww1.microchip.com/downloads/en/appnotes/00001953a.pdf pag. 10
VALID UFP RD PULL-DOWN RESISTOR VALUES
